Physical-computing-UAB/Quadruped/Documents/org/Class Diagram-2.png

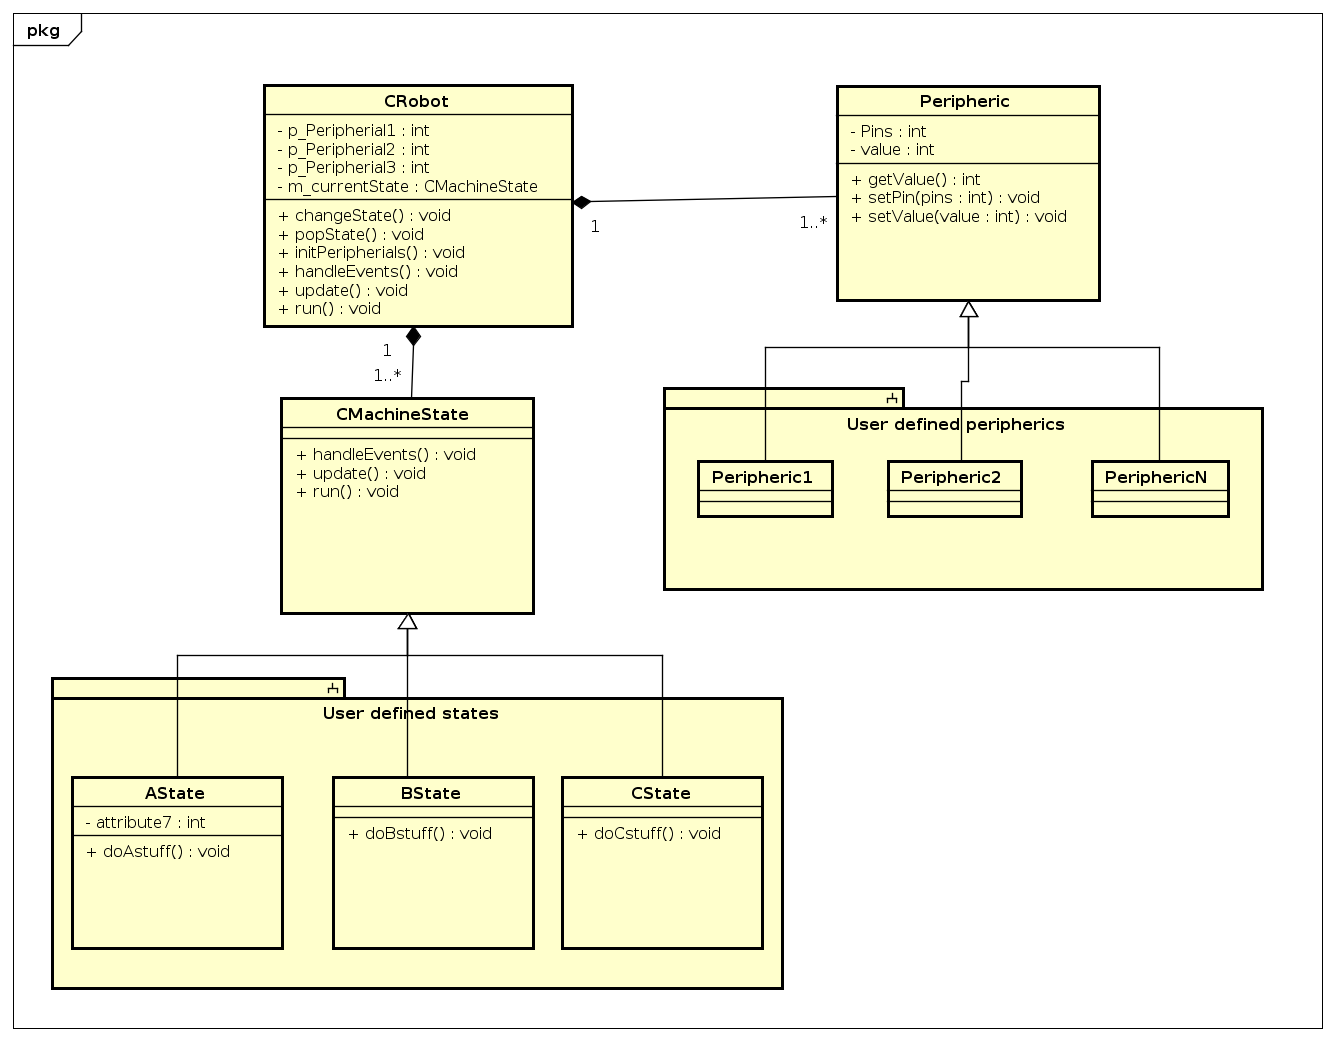
Documents/org/Class Diagram-2.png
