Physical-computing-UAB/Quadruped/Documents/org/ClassDiagram.png

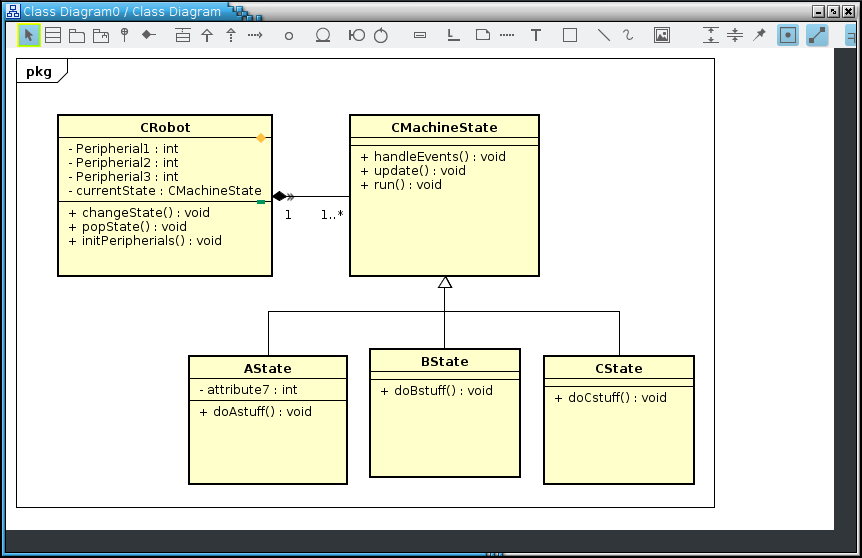
Documents/org/ClassDiagram.png
