Physical-computing-UAB/Quadruped/Documents/pics/20180621_173625.jpg

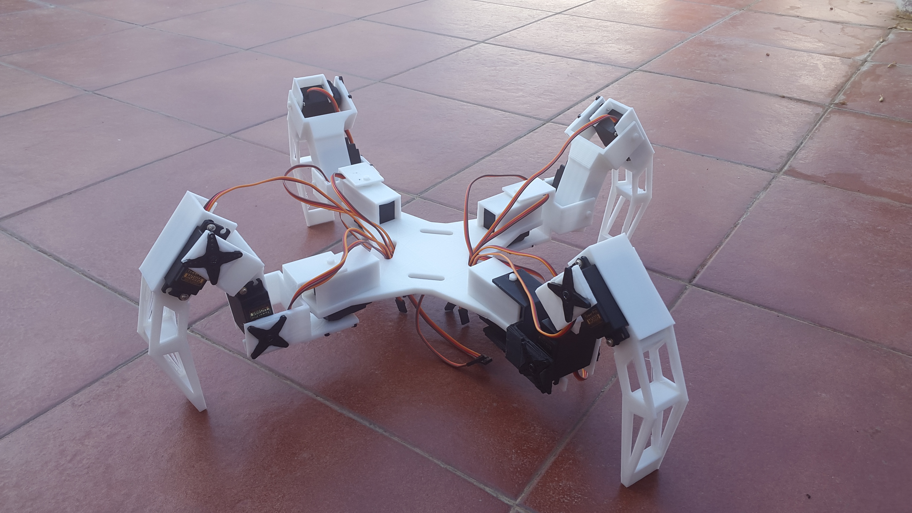
Documents/pics/20180621_173625.jpg
