Physical-computing-UAB/Quadruped/Documents/pics/20180621_173734.jpg

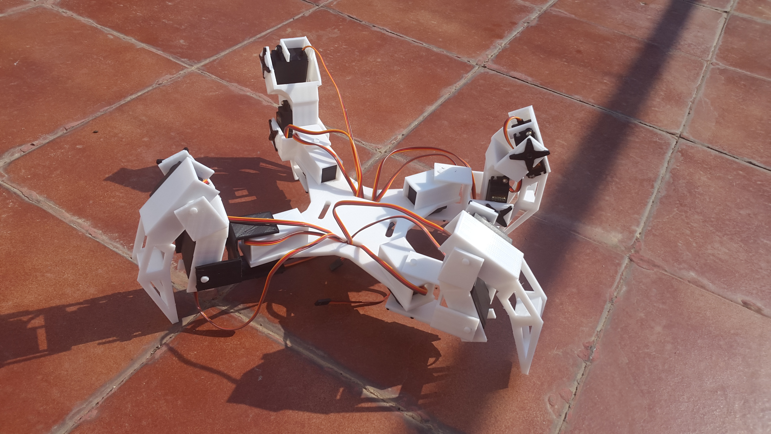
Documents/pics/20180621_173734.jpg
